dzid26/ble_stepper_motor_analyzer/platformio/src/ble/ble_host.h

#pragma once

#include "acquisition/analyzer.h"
#include <stdint.h>

namespace ble_host {

void setup(uint8_t hardware_config, uint16_t adc_ticks_per_amp);

// If state notification is enabled, send a notification with
// this state.
void notify_state_if_enabled(const analyzer::State& state);

// Returns true if a host is connected. Used also to check
// connection WDT expriation.
bool is_connected();


}  // namespace ble_host
